ifbotech/root-kit/docs/entorno.md

# Entorno y simulador

Todo el firmware se escribe y se anima en la PC. Las placas sirven para
confirmar las tres cosas que la PC no puede decir —consumo, colores reales y
framerate— no para desarrollar.

## Qué hace falta

| Componente | Versión verificada | Para qué |
|---|---|---|
| WSL2 + Ubuntu | 24.04 LTS | Todo el firmware |
| gcc | 13.3.0 | Compilar |
| GNU Make | 4.3 | Los targets |
| SDL2 | 2.30.0 | Sólo la ventana interactiva |
| WSLg | driver x11, `DISPLAY=:0` | Mostrar esa ventana en Windows |
| clang + lld | 18 | `make wasm`: el renderer para la app |
| PlatformIO | 6.1+ | Compilar y flashear las placas (`pip install platformio`) |
| Python | 3.10+ | Convertir capturas, la estación de fábrica y el sustrato (`tools/pcb.py`) |
| OpenSCAD | 2021.01+ | Exportar el STL del sustrato. Sólo para `make pcb`: el resto se genera sin él |
| Node | 20+ | root-lab: la app, la nube y el emulador |

Las pruebas y las capturas **no necesitan SDL**: el Makefile lo detecta con
`pkg-config` y compila el simulador sin ventana si no está. Sólo `make sim` lo
pide.

**OpenSCAD tampoco es obligatorio.** `make pcb` verifica el sustrato y
regenera la plantilla, el diagrama de conexiones y la netlist con Python solo;
si OpenSCAD no está, avisa y deja el STL como estaba. En Windows está en
`C:\Program Files\OpenSCAD\openscad.exe` y se usa por línea de comandos.

```bash
cd /mnt/c/Users/ifbar/Documents/rootkit/firmware
make test
```

> **La imagen de Ubuntu viene con el índice de apt desactualizado.** Si
> instalás algo y apt tira `404 Not Found` sobre paquetes de glibc, es eso:
> corré `sudo apt update` primero. Le pasa a `build-essential` en una imagen
> recién creada, porque el índice apunta a versiones que ya salieron del pool.

En Windows hay que invocar la distro por nombre si la predeterminada es otra
(por ejemplo con Docker Desktop instalado, que registra la suya):

```bash
wsl.exe -d Ubuntu-24.04 -- bash -lc "cd /mnt/c/.../firmware && make test"
```

Y una sola vez, para que `make verify` pueda usar git desde WSL sobre `/mnt/c`:

```bash
git config --global --add safe.directory /mnt/c/Users/<vos>/Documents/rootkit
```

Sin eso git falla con `dubious ownership`. Vale la pena saber por qué el
Makefile lo comprueba explícitamente: en ese estado **git escribe el error en
stderr y aun así devuelve 0**, así que el chequeo de frescura del arte leía su
salida vacía como "no hay cambios" y pasaba en verde sin haber mirado nada. El
target ahora exige que `git rev-parse --show-toplevel` devuelva algo antes de
confiar en un `git status` vacío.

## La ventana muestra los cinco Rooties

```bash
make sim
```

Los cinco Rooties en una grilla, todos animándose con el mismo reloj sobre el
mismo mundo simulado, a 2× para que se vean en un monitor.

Eso es deliberado: lo que hay que juzgar es **si los cinco se leen como el mismo
producto y como ocho personajes distintos al mismo tiempo**. El parecido y la
diferencia sólo existen en comparación, así que con una cara por vez las dos
cosas son imposibles de evaluar.

| Tecla | Qué hace |
|---|---|
| `1`–`6` | Seleccionar modelo |
| `W` | Regar la maceta seleccionada |
| `M` | Ciclar los ánimos a la fuerza |
| `R` | Volver al ánimo real |
| `G` | Disparar el despertar del seleccionado |
| `+` / `-` | Acelerar o frenar el tiempo |
| `S` | Capturar la ventana entera a `captura.bmp` |
| `ESC` | Salir |

Un día simulado dura 48 segundos. Cada maceta tiene un ambiente que deriva
solo: la tierra se seca a su ritmo y el sol sale y se pone. Sin eso el
simulador muestra estados congelados y no se puede juzgar si las transiciones
se sienten bien.

Los seis aparatos arrancan con vínculos de distinta edad —9, 34, 62, 95, 140 y
200 días sanos— para que la ventana muestre de entrada varias etapas de
crecimiento sin tener que esperar seis meses.

## Capturas sin ventana

```bash
make sheet       # los 6 modelos x 11 ánimos
make etapas      # las 5 etapas de crecimiento, por modelo
make despertar   # los ojos se abren, por modelo
make pantallas   # QR, dormida, despertar y cara
make bench       # costo de rasterizado y cota del bus
```

Escriben BMP en `firmware/build/`. `tools/bmp2png.py` los pasa a PNG para
meterlos en el repo o mirarlos en cualquier lado.

Estos modos no abren ventana, así que corren en CI. Y son la única forma de
revisar el arte con los ojos: **la regresión visual por hash detecta que algo
cambió, no si quedó mejor o peor.**

## Por qué no hay LVGL

El plan original era usar LVGL con su port de SDL. Se descartó, y las razones
están en [decisiones.md](decisiones.md). En resumen: la cara es procedural —elipses, arcos y trazos calculados— y LVGL trae un motor
de widgets que acá no se usaría nunca; y un buffer RGB565 plano es exactamente
lo que espera `esp_lcd_panel_draw_bitmap()`, sin capa intermedia.

El renderer propio vive en `gfx/`, y el mismo código corre en el simulador, en
los tests, en las placas y, compilado a WebAssembly, en la app.

## Lo que NO se puede probar acá

Anotarlo ahora evita sorpresas cuando lleguen las placas:

- **El consumo.** Es un modelo (`nodo/power.c`). El reposo real del C3 y la
  corriente de cada retroiluminación pueden mover mucho la autonomía.
  Medidor en serie, el día uno.
- **Framerate real.** La cara con antialiasing tarda ~0,5 ms por cuadro de
  128×128 en una PC; en el C3, sin FPU y a 160 MHz, puede tardar cincuenta
  veces más. Se mide en la Fase 1.
- **Colores.** El IPS no tiene el mismo gamma que un monitor. Si salen raros,
  es el orden de bytes o de colores del panel: `RK_TFT_BGR` y
  `RK_TFT_INVERT` en `platformio.ini`.
- **Cómo se ve una cara dentro de su carcasa.** No hay forma de simularlo: hay
  que imprimir.
- **El portal cautivo en cada teléfono.** Para el resto del flujo está el
  emulador de root-lab.
