ifbotech/root-kit/hardware/pcb/generado/sustrato_datos.scad

// GENERADO por tools/pcb.py desde hardware/pcb/nucleo.json. No editar.

sustrato_ancho = 68.00;
sustrato_alto  = 92.00;
sustrato_esp   = 3.00;
canaleta_prof  = 1.20;
canaleta_holg  = 0.30;
radio_borde    = 2.00;

// [ancho, [[x,y], ...]]
canaletas = [
  [1.00, [[23.40,68.80], [23.28,68.80], [19.40,68.80], [19.40,64.55], [19.40,33.00]]],  // TFT_CS
  [1.00, [[19.40,33.00], [19.08,31.95]]],  // TFT_CS
  [1.00, [[23.40,71.40], [23.28,71.40], [14.40,71.40], [14.40,64.55], [14.40,33.00]]],  // TFT_DC
  [1.00, [[14.40,33.00], [14.00,31.95]]],  // TFT_DC
  [1.00, [[23.40,79.00], [23.28,79.00], [11.40,79.00], [11.40,64.55], [11.40,33.00]]],  // MOSI
  [1.00, [[11.40,33.00], [11.46,31.95]]],  // MOSI
  [1.00, [[23.40,81.60], [23.28,81.60], [8.80,81.60], [8.80,64.55], [8.80,33.00]]],  // SCK
  [1.00, [[8.80,33.00], [8.92,31.95]]],  // SCK
  [1.00, [[23.40,66.00], [23.28,66.00], [22.20,66.00], [22.20,64.55], [22.20,32.80], [23.28,32.80], [27.00,32.80], [27.00,13.40], [23.28,13.40], [12.80,13.40], [12.80,11.40]]],  // BL_G
  [1.00, [[12.80,11.40], [12.30,10.50]]],  // BL_G
  [1.00, [[11.40,10.00], [9.60,10.00]]],  // BL_G
  [1.00, [[9.60,10.00], [9.15,10.60]]],  // BL_G
  [1.00, [[16.40,27.00], [16.40,25.00]]],  // TFT_RST
  [1.00, [[16.40,25.00], [17.30,24.00]]],  // TFT_RST
  [1.00, [[7.40,20.00], [5.00,20.00], [5.00,20.40]]],  // BL_Q
  [1.00, [[5.00,20.40], [4.00,21.30]]],  // BL_Q
  [1.00, [[8.60,14.00], [9.40,14.00], [9.40,16.00]]],  // BL_M
  [1.00, [[9.40,16.00], [9.15,16.60]]],  // BL_M
  [1.00, [[10.00,15.60], [11.40,15.60]]],  // BL_M
  [1.00, [[11.40,15.60], [12.30,16.50]]],  // BL_M
  [1.00, [[5.00,25.20], [5.20,25.20]]],  // BL
  [1.00, [[5.20,25.20], [6.40,25.20], [6.40,27.00]]],  // BL
  [1.00, [[6.40,27.00], [6.38,28.05]]],  // BL
  [1.00, [[6.80,24.80], [9.00,24.80]]],  // BL
  [1.00, [[9.00,24.80], [10.00,24.00]]],  // BL
  [1.00, [[44.60,66.00], [44.72,66.00], [47.00,66.00]]],  // SUELO
  [1.00, [[47.00,66.00], [47.46,65.95]]],  // SUELO
  [1.00, [[44.60,69.00], [44.72,69.00], [51.40,69.00], [51.40,66.80], [55.40,66.80], [55.40,64.55], [55.40,62.60]]],  // RIEL
  [1.00, [[55.40,62.60], [56.00,61.70]]],  // RIEL
  [1.00, [[44.60,71.40], [44.72,71.40], [53.40,71.40], [53.40,71.00]]],  // SENS_EN
  [1.00, [[53.40,71.00], [54.30,70.00]]],  // SENS_EN
  [1.00, [[54.80,71.00], [54.80,73.00], [62.80,73.00], [62.80,69.80]]],  // SENS_EN
  [1.00, [[62.80,69.80], [62.80,69.60]]],  // SENS_EN
  [1.00, [[62.80,69.60], [63.40,69.15]]],  // SENS_EN
  [1.00, [[52.20,46.80], [58.00,46.80]]],  // SDA
  [1.00, [[58.00,46.80], [58.46,45.95]]],  // SDA
  [1.00, [[47.00,55.00], [47.00,50.80], [45.00,50.80]]],  // OW
  [1.00, [[45.00,50.80], [44.72,50.66], [44.00,50.30]]],  // OW
  [1.40, [[60.00,67.40], [60.00,65.00]]],  // 3V3S
  [1.00, [[60.00,65.00], [60.00,64.55], [60.00,64.00]]],  // 3V3S
  [1.40, [[61.00,63.00], [61.80,63.00], [61.80,60.60], [64.00,60.60]]],  // 3V3S
  [1.00, [[64.00,60.60], [65.00,60.30]]],  // 3V3S
  [1.00, [[55.40,83.60], [55.20,83.60]]],  // VIN
  [2.20, [[55.20,83.60], [54.80,83.60], [54.80,87.45], [54.80,88.40], [62.00,88.40]]],  // VIN
  [1.00, [[62.00,88.40], [63.00,88.00]]],  // VIN
  [2.20, [[53.80,84.60], [44.72,84.60], [44.60,84.60]]],  // VIN
  [1.00, [[44.60,84.60], [43.57,84.13]]],  // VIN
  [1.20, [[44.60,79.00], [44.72,79.00], [62.40,79.00], [62.40,75.40], [66.00,75.40], [66.00,66.60], [64.00,66.60]]],  // 3V3
  [1.00, [[64.00,66.60], [63.40,66.85]]],  // 3V3
  [1.00, [[52.80,53.00], [52.80,59.00], [44.72,59.00], [44.40,59.00], [44.40,54.60]]],  // 3V3
  [1.00, [[44.40,54.60], [44.00,53.70]]],  // 3V3
  [2.20, [[43.00,53.80], [40.40,53.80], [40.40,45.20], [43.20,45.20], [43.20,42.60], [43.60,42.60]]],  // 3V3
  [1.00, [[43.60,42.60], [43.80,42.60]]],  // 3V3
  [1.00, [[43.80,42.60], [44.19,42.05]]],  // 3V3
  [1.00, [[42.60,41.60], [41.70,42.00]]],  // 3V3
  [2.20, [[39.40,45.60], [35.40,45.60]]],  // 3V3
  [1.00, [[35.40,45.60], [34.50,45.85]]],  // 3V3
  [2.20, [[33.60,44.80], [33.60,39.00], [27.00,39.00]]],  // 3V3
  [1.00, [[27.00,39.00], [26.00,38.00]]],  // 3V3
  [1.00, [[24.20,27.00], [24.20,25.00], [23.28,25.00], [21.60,25.00]]],  // 3V3
  [1.00, [[21.60,25.00], [20.70,24.00]]],  // 3V3
  [2.20, [[20.80,23.00], [20.80,17.40], [16.60,17.40]]],  // 3V3
  [1.00, [[16.60,17.40], [15.70,16.50]]],  // 3V3
  [2.20, [[43.60,41.40], [43.60,28.40], [44.72,28.40], [53.00,28.40], [53.00,31.00]]],  // 3V3
  [1.00, [[53.00,31.00], [52.54,32.05]]],  // 3V3
  [1.00, [[53.00,33.00], [66.00,33.00], [66.00,41.00]]],  // 3V3
  [1.00, [[66.00,41.00], [66.08,42.05]]],  // 3V3
  [2.20, [[59.60,53.40], [59.60,50.20], [57.00,50.20]]],  // GND
  [1.00, [[57.00,50.20], [56.00,50.30]]],  // GND
  [1.00, [[47.20,41.00], [47.20,39.00], [63.20,39.00], [63.20,41.00]]],  // GND
  [1.00, [[63.20,41.00], [63.54,42.05]]],  // GND
  [2.20, [[28.40,49.20], [28.40,45.00], [27.00,45.00]]],  // GND
  [1.00, [[27.00,45.00], [26.00,44.00]]],  // GND
  [2.20, [[37.40,41.00], [37.40,10.20], [23.28,10.20], [16.60,10.20]]],  // GND
  [1.00, [[16.60,10.20], [15.70,10.50]]],  // GND
  [1.20, [[15.20,9.60], [15.20,7.40], [6.60,7.40], [6.60,10.00]]],  // GND
  [1.00, [[6.60,10.00], [6.85,10.60]]],  // GND
];

// [x, y, ancho, alto, rot, agujero]
pads = [
  [60.00,54.30,2.00,1.90,0.0,0.00],  // C1.1
  [60.00,57.70,2.00,1.90,0.0,0.00],  // C1.2
  [29.50,50.15,2.20,2.20,0.0,2.10],  // C2.1
  [34.50,45.85,2.20,2.20,0.0,2.10],  // C2.2
  [38.30,42.00,1.90,2.00,0.0,0.00],  // C3.1
  [41.70,42.00,1.90,2.00,0.0,0.00],  // C3.2
  [65.00,52.30,2.00,1.90,0.0,0.00],  // C4.1
  [65.00,55.70,2.00,1.90,0.0,0.00],  // C4.2
  [46.73,42.05,1.00,2.20,0.0,1.70],  // J_AIRE.GND
  [49.27,45.95,1.00,2.20,0.0,1.70],  // J_AIRE.SCL
  [51.81,45.95,1.00,2.20,0.0,1.70],  // J_AIRE.SDA
  [44.19,42.05,1.00,2.20,0.0,1.70],  // J_AIRE.VCC
  [55.92,42.05,1.00,2.20,180.0,1.70],  // J_LUZ.ADDR
  [63.54,42.05,1.00,2.20,180.0,1.70],  // J_LUZ.GND
  [61.00,45.95,1.00,2.20,180.0,1.70],  // J_LUZ.SCL
  [58.46,45.95,1.00,2.20,180.0,1.70],  // J_LUZ.SDA
  [66.08,42.05,1.00,2.20,180.0,1.70],  // J_LUZ.VCC
  [58.27,83.05,1.00,2.20,0.0,1.70],  // J_PWR.GND
  [55.73,83.05,1.00,2.20,0.0,1.70],  // J_PWR.VIN
  [47.46,65.95,1.00,2.20,0.0,1.70],  // J_SUELO.AOUT
  [50.00,62.05,1.00,2.20,0.0,1.70],  // J_SUELO.GND
  [52.54,62.05,1.00,2.20,0.0,1.70],  // J_SUELO.VCC
  [19.08,31.95,1.00,2.20,180.0,1.70],  // J_TFT.CS
  [14.00,31.95,1.00,2.20,180.0,1.70],  // J_TFT.DC
  [21.62,28.05,1.00,2.20,180.0,1.70],  // J_TFT.GND
  [6.38,28.05,1.00,2.20,180.0,1.70],  // J_TFT.LED
  [16.54,28.05,1.00,2.20,180.0,1.70],  // J_TFT.RESET
  [8.92,31.95,1.00,2.20,180.0,1.70],  // J_TFT.SCK
  [11.46,31.95,1.00,2.20,180.0,1.70],  // J_TFT.SDI
  [3.84,28.05,1.00,2.20,180.0,1.70],  // J_TFT.SDO
  [24.16,28.05,1.00,2.20,180.0,1.70],  // J_TFT.VCC
  [47.46,55.95,1.00,2.20,0.0,1.70],  // J_TIERRA.DQ
  [50.00,52.05,1.00,2.20,0.0,1.70],  // J_TIERRA.GND
  [52.54,52.05,1.00,2.20,0.0,1.70],  // J_TIERRA.VCC
  [50.00,32.05,1.00,2.20,0.0,1.70],  // J_TOQUE.GND
  [47.46,35.95,1.00,2.20,0.0,1.70],  // J_TOQUE.IO
  [52.54,32.05,1.00,2.20,0.0,1.70],  // J_TOQUE.VCC
  [60.60,68.00,1.20,1.40,270.0,0.00],  // Q2.D
  [63.40,69.15,1.20,1.40,270.0,0.00],  // Q2.G
  [63.40,66.85,1.20,1.40,270.0,0.00],  // Q2.S
  [8.00,13.40,1.20,1.40,180.0,0.00],  // Q3.D
  [9.15,10.60,1.20,1.40,180.0,0.00],  // Q3.G
  [6.85,10.60,1.20,1.40,180.0,0.00],  // Q3.S
  [8.00,19.40,1.20,1.40,180.0,0.00],  // Q4.D
  [9.15,16.60,1.20,1.40,180.0,0.00],  // Q4.G
  [6.85,16.60,1.20,1.40,180.0,0.00],  // Q4.S
  [56.00,58.30,2.00,1.90,0.0,0.00],  // R1.1
  [56.00,61.70,2.00,1.90,0.0,0.00],  // R1.2
  [4.00,21.30,2.00,1.90,0.0,0.00],  // R11.1
  [4.00,24.70,2.00,1.90,0.0,0.00],  // R11.2
  [56.00,50.30,2.00,1.90,0.0,0.00],  // R2.1
  [56.00,53.70,2.00,1.90,0.0,0.00],  // R2.2
  [54.30,70.00,1.90,2.00,0.0,0.00],  // R4.1
  [57.70,70.00,1.90,2.00,0.0,0.00],  // R4.2
  [65.00,60.30,2.00,1.90,0.0,0.00],  // R5.1
  [65.00,63.70,2.00,1.90,0.0,0.00],  // R5.2
  [44.00,50.30,2.00,1.90,0.0,0.00],  // R6.1
  [44.00,53.70,2.00,1.90,0.0,0.00],  // R6.2
  [17.30,24.00,1.90,2.00,0.0,0.00],  // R7.1
  [20.70,24.00,1.90,2.00,0.0,0.00],  // R7.2
  [12.30,10.50,1.90,2.00,0.0,0.00],  // R8.1
  [15.70,10.50,1.90,2.00,0.0,0.00],  // R8.2
  [12.30,16.50,1.90,2.00,0.0,0.00],  // R9.1
  [15.70,16.50,1.90,2.00,0.0,0.00],  // R9.2
  [26.00,44.00,2.20,2.20,0.0,0.00],  // TP1.1
  [63.00,88.00,2.20,2.20,0.0,0.00],  // TP2.1
  [26.00,38.00,2.20,2.20,0.0,0.00],  // TP3.1
  [60.00,64.00,2.20,2.20,0.0,0.00],  // TP4.1
  [10.00,24.00,2.20,2.20,0.0,0.00],  // TP5.1
  [43.57,79.05,2.20,1.00,0.0,1.70],  // U1.3V3
  [43.57,84.13,2.20,1.00,0.0,1.70],  // U1.5V
  [43.57,81.59,2.20,1.00,0.0,1.70],  // U1.GND
  [43.57,66.35,2.20,1.00,0.0,1.70],  // U1.IO0
  [43.57,68.89,2.20,1.00,0.0,1.70],  // U1.IO1
  [24.43,71.43,2.20,1.00,0.0,1.70],  // U1.IO10
  [43.57,71.43,2.20,1.00,0.0,1.70],  // U1.IO2
  [24.43,68.89,2.20,1.00,0.0,1.70],  // U1.IO20
  [24.43,66.35,2.20,1.00,0.0,1.70],  // U1.IO21
  [43.57,73.97,2.20,1.00,0.0,1.70],  // U1.IO3
  [43.57,76.51,2.20,1.00,0.0,1.70],  // U1.IO4
  [24.43,84.13,2.20,1.00,0.0,1.70],  // U1.IO5
  [24.43,81.59,2.20,1.00,0.0,1.70],  // U1.IO6
  [24.43,79.05,2.20,1.00,0.0,1.70],  // U1.IO7
  [24.43,76.51,2.20,1.00,0.0,1.70],  // U1.IO8
  [24.43,73.97,2.20,1.00,0.0,1.70],  // U1.IO9
];

// [centro x, centro y, ancho, alto] — aberturas pasantes
recortes = [
  [34.00,87.67,9.00,9.00],  // antena
];

// [x, y, diametro]
tornillos = [
  [3.00,11.00,2.70],
  [65.00,11.00,2.70],
  [3.00,81.00,2.70],
  [65.00,81.00,2.70],
];

// --- la estampadora (el negativo, espejado en X) ---
est_holgura_lateral = 0.20;
est_sobresalir     = 1.00;
est_base_extra     = 0.20;
est_base_alto      = 0.25;
est_espesor        = 5.00;
est_faldon_alto    = 3.50;
est_faldon_pared   = 2.00;
est_faldon_holgura = 0.50;
est_relieve_hueco  = 0.60;
est_rotulo_tam   = 5.00;
est_rotulo       = "ESTAMPADORA v3.1";

// [x, y, tamano, rot, "texto"]
rotulos = [
  [31.00,58.00,2.00,0.0,"ROOTKIT v3.0"],
  [31.00,53.50,1.60,0.0,"ifbotech"],
];
