ifbotech/root-kit/firmware/esp32/certificados.h

/* certificados.h — las raíces en las que confía la placa para hablar con la nube.
 *
 * GENERADO a partir del almacén de certificados de Ubuntu y de
 * letsencrypt.org/certificates. Ver docs/firmware.md, "La nube por HTTPS".
 *
 * El servidor de ROOTLAB (Caddy) saca sus certificados de Let's Encrypt y,
 * si Let's Encrypt falla, de ZeroSSL. La placa confía SOLO en las raíces de
 * esas dos autoridades: un certificado de cualquier otra —aunque un
 * navegador lo acepte— no alcanza para hacerse pasar por la nube.
 *
 * Van también las raíces de la generación siguiente de Let's Encrypt (Root
 * YE y YR): una placa se queda años en una casa, y tiene que seguir
 * conectándose cuando cambie la cadena.
 *
 * Huellas SHA-256, para verificar contra las que publica cada autoridad:
 *
 *   ISRG Root X1 (Let's Encrypt, RSA, vence 2035)
 *     96:BC:EC:06:26:49:76:F3:74:60:77:9A:CF:28:C5:A7:CF:E8:A3:C0:AA:E1:1A:8F:FC:EE:05:C0:BD:DF:08:C6
 *   ISRG Root X2 (Let's Encrypt, ECDSA, vence 2040)
 *     69:72:9B:8E:15:A8:6E:FC:17:7A:57:AF:B7:17:1D:FC:64:AD:D2:8C:2F:CA:8C:F1:50:7E:34:45:3C:CB:14:70
 *   ISRG Root YE (Let's Encrypt, generacion Y, ECDSA, vence 2045)
 *     E1:4F:FC:AD:5B:00:25:73:10:06:CA:A4:3A:12:1A:22:D8:E9:70:0F:4F:B9:CF:85:2F:02:A7:08:AA:5D:56:66
 *   ISRG Root YR (Let's Encrypt, generacion Y, RSA, vence 2045)
 *     E5:7B:7E:6F:15:0C:41:91:02:E8:D5:C0:55:72:9F:F9:67:B9:D1:A8:29:BF:00:CE:C8:9C:A6:04:EB:F4:A8:6F
 *   USERTrust ECC (ZeroSSL, la CA de respaldo de Caddy, vence 2038)
 *     4F:F4:60:D5:4B:9C:86:DA:BF:BC:FC:57:12:E0:40:0D:2B:ED:3F:BC:4D:4F:BD:AA:86:E0:6A:DC:D2:A9:AD:7A
 *   USERTrust RSA (ZeroSSL, vence 2038)
 *     E7:93:C9:B0:2F:D8:AA:13:E2:1C:31:22:8A:CC:B0:81:19:64:3B:74:9C:89:89:64:B1:74:6D:46:C3:D4:CB:D2
 */
#ifndef ROOTKIT_CERTIFICADOS_H
#define ROOTKIT_CERTIFICADOS_H

static const char RK_CA_RAICES[] =
    /* ISRG Root X1 (Let's Encrypt, RSA, vence 2035) */
    "-----BEGIN CERTIFICATE-----\n"
    "MIIFazCCA1OgAwIBAgIRAIIQz7DSQONZRGPgu2OCiwAwDQYJKoZIhvcNAQELBQAw\n"
    "TzELMAkGA1UEBhMCVVMxKTAnBgNVBAoTIEludGVybmV0IFNlY3VyaXR5IFJlc2Vh\n"
    "cmNoIEdyb3VwMRUwEwYDVQQDEwxJU1JHIFJvb3QgWDEwHhcNMTUwNjA0MTEwNDM4\n"
    "WhcNMzUwNjA0MTEwNDM4WjBPMQswCQYDVQQGEwJVUzEpMCcGA1UEChMgSW50ZXJu\n"
    "ZXQgU2VjdXJpdHkgUmVzZWFyY2ggR3JvdXAxFTATBgNVBAMTDElTUkcgUm9vdCBY\n"
    "MTCCAiIwDQYJKoZIhvcNAQEBBQADggIPADCCAgoCggIBAK3oJHP0FDfzm54rVygc\n"
    "h77ct984kIxuPOZXoHj3dcKi/vVqbvYATyjb3miGbESTtrFj/RQSa78f0uoxmyF+\n"
    "0TM8ukj13Xnfs7j/EvEhmkvBioZxaUpmZmyPfjxwv60pIgbz5MDmgK7iS4+3mX6U\n"
    "A5/TR5d8mUgjU+g4rk8Kb4Mu0UlXjIB0ttov0DiNewNwIRt18jA8+o+u3dpjq+sW\n"
    "T8KOEUt+zwvo/7V3LvSye0rgTBIlDHCNAymg4VMk7BPZ7hm/ELNKjD+Jo2FR3qyH\n"
    "B5T0Y3HsLuJvW5iB4YlcNHlsdu87kGJ55tukmi8mxdAQ4Q7e2RCOFvu396j3x+UC\n"
    "B5iPNgiV5+I3lg02dZ77DnKxHZu8A/lJBdiB3QW0KtZB6awBdpUKD9jf1b0SHzUv\n"
    "KBds0pjBqAlkd25HN7rOrFleaJ1/ctaJxQZBKT5ZPt0m9STJEadao0xAH0ahmbWn\n"
    "OlFuhjuefXKnEgV4We0+UXgVCwOPjdAvBbI+e0ocS3MFEvzG6uBQE3xDk3SzynTn\n"
    "jh8BCNAw1FtxNrQHusEwMFxIt4I7mKZ9YIqioymCzLq9gwQbooMDQaHWBfEbwrbw\n"
    "qHyGO0aoSCqI3Haadr8faqU9GY/rOPNk3sgrDQoo//fb4hVC1CLQJ13hef4Y53CI\n"
    "rU7m2Ys6xt0nUW7/vGT1M0NPAgMBAAGjQjBAMA4GA1UdDwEB/wQEAwIBBjAPBgNV\n"
    "HRMBAf8EBTADAQH/MB0GA1UdDgQWBBR5tFnme7bl5AFzgAiIyBpY9umbbjANBgkq\n"
    "hkiG9w0BAQsFAAOCAgEAVR9YqbyyqFDQDLHYGmkgJykIrGF1XIpu+ILlaS/V9lZL\n"
    "ubhzEFnTIZd+50xx+7LSYK05qAvqFyFWhfFQDlnrzuBZ6brJFe+GnY+EgPbk6ZGQ\n"
    "3BebYhtF8GaV0nxvwuo77x/Py9auJ/GpsMiu/X1+mvoiBOv/2X/qkSsisRcOj/KK\n"
    "NFtY2PwByVS5uCbMiogziUwthDyC3+6WVwW6LLv3xLfHTjuCvjHIInNzktHCgKQ5\n"
    "ORAzI4JMPJ+GslWYHb4phowim57iaztXOoJwTdwJx4nLCgdNbOhdjsnvzqvHu7Ur\n"
    "TkXWStAmzOVyyghqpZXjFaH3pO3JLF+l+/+sKAIuvtd7u+Nxe5AW0wdeRlN8NwdC\n"
    "jNPElpzVmbUq4JUagEiuTDkHzsxHpFKVK7q4+63SM1N95R1NbdWhscdCb+ZAJzVc\n"
    "oyi3B43njTOQ5yOf+1CceWxG1bQVs5ZufpsMljq4Ui0/1lvh+wjChP4kqKOJ2qxq\n"
    "4RgqsahDYVvTH9w7jXbyLeiNdd8XM2w9U/t7y0Ff/9yi0GE44Za4rF2LN9d11TPA\n"
    "mRGunUHBcnWEvgJBQl9nJEiU0Zsnvgc/ubhPgXRR4Xq37Z0j4r7g1SgEEzwxA57d\n"
    "emyPxgcYxn/eR44/KJ4EBs+lVDR3veyJm+kXQ99b21/+jh5Xos1AnX5iItreGCc=\n"
    "-----END CERTIFICATE-----\n"
    /* ISRG Root X2 (Let's Encrypt, ECDSA, vence 2040) */
    "-----BEGIN CERTIFICATE-----\n"
    "MIICGzCCAaGgAwIBAgIQQdKd0XLq7qeAwSxs6S+HUjAKBggqhkjOPQQDAzBPMQsw\n"
    "CQYDVQQGEwJVUzEpMCcGA1UEChMgSW50ZXJuZXQgU2VjdXJpdHkgUmVzZWFyY2gg\n"
    "R3JvdXAxFTATBgNVBAMTDElTUkcgUm9vdCBYMjAeFw0yMDA5MDQwMDAwMDBaFw00\n"
    "MDA5MTcxNjAwMDBaME8xCzAJBgNVBAYTAlVTMSkwJwYDVQQKEyBJbnRlcm5ldCBT\n"
    "ZWN1cml0eSBSZXNlYXJjaCBHcm91cDEVMBMGA1UEAxMMSVNSRyBSb290IFgyMHYw\n"
    "EAYHKoZIzj0CAQYFK4EEACIDYgAEzZvVn4CDCuwJSvMWSj5cz3es3mcFDR0HttwW\n"
    "+1qLFNvicWDEukWVEYmO6gbf9yoWHKS5xcUy4APgHoIYOIvXRdgKam7mAHf7AlF9\n"
    "ItgKbppbd9/w+kHsOdx1ymgHDB/qo0IwQDAOBgNVHQ8BAf8EBAMCAQYwDwYDVR0T\n"
    "AQH/BAUwAwEB/zAdBgNVHQ4EFgQUfEKWrt5LSDv6kviejM9ti6lyN5UwCgYIKoZI\n"
    "zj0EAwMDaAAwZQIwe3lORlCEwkSHRhtFcP9Ymd70/aTSVaYgLXTWNLxBo1BfASdW\n"
    "tL4ndQavEi51mI38AjEAi/V3bNTIZargCyzuFJ0nN6T5U6VR5CmD1/iQMVtCnwr1\n"
    "/q4AaOeMSQ+2b1tbFfLn\n"
    "-----END CERTIFICATE-----\n"
    /* ISRG Root YE (Let's Encrypt, generacion Y, ECDSA, vence 2045) */
    "-----BEGIN CERTIFICATE-----\n"
    "MIIB2TCCAWCgAwIBAgIRAKQCa6LvbHwg1AR+XmWmk4AwCgYIKoZIzj0EAwMwLjEL\n"
    "MAkGA1UEBhMCVVMxDTALBgNVBAoTBElTUkcxEDAOBgNVBAMTB1Jvb3QgWUUwHhcN\n"
    "MjUwOTAzMDAwMDAwWhcNNDUwOTAyMjM1OTU5WjAuMQswCQYDVQQGEwJVUzENMAsG\n"
    "A1UEChMESVNSRzEQMA4GA1UEAxMHUm9vdCBZRTB2MBAGByqGSM49AgEGBSuBBAAi\n"
    "A2IABDwS/6vhrcVqcbBo+wgdI3fwn9x7DNJJOY/lTOti0vkwuRN87RhEhTH17E7X\n"
    "yFjWsPYhIPt/wzOqxTd2b+4ZJNy9ID04YywF9U5zasDVyGSNErVNtz8uSGh5izW8\n"
    "7j77GaNCMEAwDgYDVR0PAQH/BAQDAgEGMA8GA1UdEwEB/wQFMAMBAf8wHQYDVR0O\n"
    "BBYEFKPIJlqOoUzQNWP8myPIOq5W809WMAoGCCqGSM49BAMDA2cAMGQCMHhMr8N9\n"
    "LdL1VQKs9BdV81r76eXRB6mtjuNjzk6/lBsPNToWLTDzGYgtQKO1jl63uAIwGV7m\n"
    "onyF377c+MM1oqVNs17sgu7F9YKZwgLmVbeOMDbKAXHtKMDLbiGllCcs8f47\n"
    "-----END CERTIFICATE-----\n"
    /* ISRG Root YR (Let's Encrypt, generacion Y, RSA, vence 2045) */
    "-----BEGIN CERTIFICATE-----\n"
    "MIIFKTCCAxGgAwIBAgIRAOxGNJNgz0sP+KmC2Tqpyj0wDQYJKoZIhvcNAQELBQAw\n"
    "LjELMAkGA1UEBhMCVVMxDTALBgNVBAoTBElTUkcxEDAOBgNVBAMTB1Jvb3QgWVIw\n"
    "HhcNMjUwOTAzMDAwMDAwWhcNNDUwOTAyMjM1OTU5WjAuMQswCQYDVQQGEwJVUzEN\n"
    "MAsGA1UEChMESVNSRzEQMA4GA1UEAxMHUm9vdCBZUjCCAiIwDQYJKoZIhvcNAQEB\n"
    "BQADggIPADCCAgoCggIBANvGJnN78CTJdWL3+eGfsLN5TrNBJs+VH9hRXqRbwxu9\n"
    "sGNiB0BD1fcOxbSUQCJIM1xE13Db+5Cw1w0s0EBYsvuIP/6joF0w8cuImbgR1OGg\n"
    "YbSQ4OpzI+DG8SGuTlcE873OCS+kh3srlo6vl43M5OJg4Aeo1sfHp6kTJDoIiFBN\n"
    "JAY+OKfX/FUvYKuhjT+no49lmqmupSBI5PkBQiqrEGtWU5uxU/cQWHGu8jSjFBzn\n"
    "ZqvbNPLMXMLFxCb3WTfrJBXXjqvWG+v4bjzxjjeAtOlU7qarRDvNOyAuQYLln904\n"
    "M+faKx8hnLCpJ15ZqaEgcNlY+9MMWcC5yvL2A2j3l9+2buggZX+dOE91zYmIdawT\n"
    "vSZuVvlbRrAlLxIB6pwMBjneXCjYQ8+3BCCjssbSNpZU3hTcBDdhfAlEDlYr6pEa\n"
    "tnMdmDT5BqnKC92bd0EhM1fbLHioLccLCuievT8ZkPhZrq7Mii7gNXAcUEAR8+lz\n"
    "Yal+9zTg7C5DALyVOeG/CqfRAMn1KSHCR0NSA6P8tn/mGRlnCct5rtVCLnVySVpU\n"
    "6H1qGg3DgTOuskf8eahTMiYbI5ezPJmO5ertalskQ1utp74+eDy92PI4ftHKTbq9\n"
    "IWhH4YZKh3WnJEIt+oQvlYZbY8tpEroKrFB6PFGzrJIDRyts4HqvuH52RFj2zv/B\n"
    "AgMBAAGjQjBAMA4GA1UdDwEB/wQEAwIBBjAPBgNVHRMBAf8EBTADAQH/MB0GA1Ud\n"
    "DgQWBBTe51tg0CJtQCh9Pw0B/qS1UrRRlDANBgkqhkiG9w0BAQsFAAOCAgEAWHnf\n"
    "713Bdkq7t5yN2dNIgQakUb94X9WuyhMEHHkgx4oDpSUlnG0w4g94MoqaEUE31ZjR\n"
    "LU7L5LD1g9ujFHTQu8AD215AHMVQFbm6j8hQxdXHAzDajFNQnOlDJrLjzIx176oy\n"
    "AjvUtejZx2NNmdb5fd0WGVGsCdoAJ3N8ozo7ajE8t6vfxStZb4BQ9WYJGHUDrv2N\n"
    "i5tJF6CNiPnlzs3BUfECRbE4JSk+jvy8+VoGiFE8qsH/j78x2fjgQhAQFV7P7Zxy\n"
    "dBTZ1wEkNpZNW2qnaK1SKBLa+xf6E06YRIq5uaI+HWH8SY1y5VbRgzq40EKg3yxP\n"
    "06fz+uYAUIFJoLNfhwRCc3Q6pQVuMX3yAjHAes4gk4moGcLQ5p7HAh39yeylZc1J\n"
    "41sx/jKwLIkPE6Rr1Nf4pxdsxf9SA4yOEiAkDgq04DVxn8hgYFdUtBCuiuVC2heA\n"
    "EiqVEa+8QZjuw8Gj0EbHXcRd1nInvGqRS1o9Is7YBdQN57X1AYveGBNNqjICSb7c\n"
    "awuw1EawTDrs13VUlJVEsbQ0/O/1aaV73mCdOQ8azqL2KTv1Ewu1xbquE2S+kdQU\n"
    "To9TUwat3wUA6cwXh1EfpS/3fJ0aGah5hdpRyoCLDlsSn8tkrjMfFFX0viC+GxHc\n"
    "sI1ANRYvqSFC2X1VRZfDg+wD6E21BccmifG4yWc=\n"
    "-----END CERTIFICATE-----\n"
    /* USERTrust ECC (ZeroSSL, la CA de respaldo de Caddy, vence 2038) */
    "-----BEGIN CERTIFICATE-----\n"
    "MIICjzCCAhWgAwIBAgIQXIuZxVqUxdJxVt7NiYDMJjAKBggqhkjOPQQDAzCBiDEL\n"
    "MAkGA1UEBhMCVVMxEzARBgNVBAgTCk5ldyBKZXJzZXkxFDASBgNVBAcTC0plcnNl\n"
    "eSBDaXR5MR4wHAYDVQQKExVUaGUgVVNFUlRSVVNUIE5ldHdvcmsxLjAsBgNVBAMT\n"
    "JVVTRVJUcnVzdCBFQ0MgQ2VydGlmaWNhdGlvbiBBdXRob3JpdHkwHhcNMTAwMjAx\n"
    "MDAwMDAwWhcNMzgwMTE4MjM1OTU5WjCBiDELMAkGA1UEBhMCVVMxEzARBgNVBAgT\n"
    "Ck5ldyBKZXJzZXkxFDASBgNVBAcTC0plcnNleSBDaXR5MR4wHAYDVQQKExVUaGUg\n"
    "VVNFUlRSVVNUIE5ldHdvcmsxLjAsBgNVBAMTJVVTRVJUcnVzdCBFQ0MgQ2VydGlm\n"
    "aWNhdGlvbiBBdXRob3JpdHkwdjAQBgcqhkjOPQIBBgUrgQQAIgNiAAQarFRaqflo\n"
    "I+d61SRvU8Za2EurxtW20eZzca7dnNYMYf3boIkDuAUU7FfO7l0/4iGzzvfUinng\n"
    "o4N+LZfQYcTxmdwlkWOrfzCjtHDix6EznPO/LlxTsV+zfTJ/ijTjeXmjQjBAMB0G\n"
    "A1UdDgQWBBQ64QmG1M8ZwpZ2dEl23OA1xmNjmjAOBgNVHQ8BAf8EBAMCAQYwDwYD\n"
    "VR0TAQH/BAUwAwEB/zAKBggqhkjOPQQDAwNoADBlAjA2Z6EWCNzklwBBHU6+4WMB\n"
    "zzuqQhFkoJ2UOQIReVx7Hfpkue4WQrO/isIJxOzksU0CMQDpKmFHjFJKS04YcPbW\n"
    "RNZu9YO6bVi9JNlWSOrvxKJGgYhqOkbRqZtNyWHa0V1Xahg=\n"
    "-----END CERTIFICATE-----\n"
    /* USERTrust RSA (ZeroSSL, vence 2038) */
    "-----BEGIN CERTIFICATE-----\n"
    "MIIF3jCCA8agAwIBAgIQAf1tMPyjylGoG7xkDjUDLTANBgkqhkiG9w0BAQwFADCB\n"
    "iDELMAkGA1UEBhMCVVMxEzARBgNVBAgTCk5ldyBKZXJzZXkxFDASBgNVBAcTC0pl\n"
    "cnNleSBDaXR5MR4wHAYDVQQKExVUaGUgVVNFUlRSVVNUIE5ldHdvcmsxLjAsBgNV\n"
    "BAMTJVVTRVJUcnVzdCBSU0EgQ2VydGlmaWNhdGlvbiBBdXRob3JpdHkwHhcNMTAw\n"
    "MjAxMDAwMDAwWhcNMzgwMTE4MjM1OTU5WjCBiDELMAkGA1UEBhMCVVMxEzARBgNV\n"
    "BAgTCk5ldyBKZXJzZXkxFDASBgNVBAcTC0plcnNleSBDaXR5MR4wHAYDVQQKExVU\n"
    "aGUgVVNFUlRSVVNUIE5ldHdvcmsxLjAsBgNVBAMTJVVTRVJUcnVzdCBSU0EgQ2Vy\n"
    "dGlmaWNhdGlvbiBBdXRob3JpdHkwggIiMA0GCSqGSIb3DQEBAQUAA4ICDwAwggIK\n"
    "AoICAQCAEmUXNg7D2wiz0KxXDXbtzSfTTK1Qg2HiqiBNCS1kCdzOiZ/MPans9s/B\n"
    "3PHTsdZ7NygRK0faOca8Ohm0X6a9fZ2jY0K2dvKpOyuR+OJv0OwWIJAJPuLodMkY\n"
    "tJHUYmTbf6MG8YgYapAiPLz+E/CHFHv25B+O1ORRxhFnRghRy4YUVD+8M/5+bJz/\n"
    "Fp0YvVGONaanZshyZ9shZrHUm3gDwFA66Mzw3LyeTP6vBZY1H1dat//O+T23LLb2\n"
    "VN3I5xI6Ta5MirdcmrS3ID3KfyI0rn47aGYBROcBTkZTmzNg95S+UzeQc0PzMsNT\n"
    "79uq/nROacdrjGCT3sTHDN/hMq7MkztReJVni+49Vv4M0GkPGw/zJSZrM233bkf6\n"
    "c0Plfg6lZrEpfDKEY1WJxA3Bk1QwGROs0303p+tdOmw1XNtB1xLaqUkL39iAigmT\n"
    "Yo61Zs8liM2EuLE/pDkP2QKe6xJMlXzzawWpXhaDzLhn4ugTncxbgtNMs+1b/97l\n"
    "c6wjOy0AvzVVdAlJ2ElYGn+SNuZRkg7zJn0cTRe8yexDJtC/QV9AqURE9JnnV4ee\n"
    "UB9XVKg+/XRjL7FQZQnmWEIuQxpMtPAlR1n6BB6T1CZGSlCBst6+eLf8ZxXhyVeE\n"
    "Hg9j1uliutZfVS7qXMYoCAQlObgOK6nyTJccBz8NUvXt7y+CDwIDAQABo0IwQDAd\n"
    "BgNVHQ4EFgQUU3m/WqorSs9UgOHYm8Cd8rIDZsswDgYDVR0PAQH/BAQDAgEGMA8G\n"
    "A1UdEwEB/wQFMAMBAf8wDQYJKoZIhvcNAQEMBQADggIBAFzUfA3P9wF9QZllDHPF\n"
    "Up/L+M+ZBn8b2kMVn54CVVeWFPFSPCeHlCjtHzoBN6J2/FNQwISbxmtOuowhT6KO\n"
    "VWKR82kV2LyI48SqC/3vqOlLVSoGIG1VeCkZ7l8wXEskEVX/JJpuXior7gtNn3/3\n"
    "ATiUFJVDBwn7YKnuHKsSjKCaXqeYalltiz8I+8jRRa8YFWSQEg9zKC7F4iRO/Fjs\n"
    "8PRF/iKz6y+O0tlFYQXBl2+odnKPi4w2r78NBc5xjeambx9spnFixdjQg3IM8WcR\n"
    "iQycE0xyNN+81XHfqnHd4blsjDwSXWXavVcStkNr/+XeTWYRUc+ZruwXtuhxkYze\n"
    "Sf7dNXGiFSeUHM9h4ya7b6NnJSFd5t0dCy5oGzuCr+yDZ4XUmFF0sbmZgIn/f3gZ\n"
    "XHlKYC6SQK5MNyosycdiyA5d9zZbyuAlJQG03RoHnHcAP9Dc1ew91Pq7P8yF1m9/\n"
    "qS3fuQL39ZeatTXaw2ewh0qpKJ4jjv9cJ2vhsE/zB+4ALtRZh8tSQZXq9EfX7mRB\n"
    "VXyNWQKV3WKdwrnuWih0hKWbt5DHDAff9Yk2dDLWKMGwsAvgnEzDHNb842m1R0aB\n"
    "L6KCq9NjRHDEjf8tM7qtj3u1cIiuPhnPQCjY/MiQu12ZIvVS5ljFH4gxQ+6IHdfG\n"
    "jjxDah2nGN59PRbxYvnKkKj9\n"
    "-----END CERTIFICATE-----\n";

#endif /* ROOTKIT_CERTIFICADOS_H */
