ifbotech/root-kit/firmware/core/sha256.c

#include "sha256.h"
#include <string.h>

static const uint32_t K[64] = {
    0x428a2f98u, 0x71374491u, 0xb5c0fbcfu, 0xe9b5dba5u, 0x3956c25bu, 0x59f111f1u,
    0x923f82a4u, 0xab1c5ed5u, 0xd807aa98u, 0x12835b01u, 0x243185beu, 0x550c7dc3u,
    0x72be5d74u, 0x80deb1feu, 0x9bdc06a7u, 0xc19bf174u, 0xe49b69c1u, 0xefbe4786u,
    0x0fc19dc6u, 0x240ca1ccu, 0x2de92c6fu, 0x4a7484aau, 0x5cb0a9dcu, 0x76f988dau,
    0x983e5152u, 0xa831c66du, 0xb00327c8u, 0xbf597fc7u, 0xc6e00bf3u, 0xd5a79147u,
    0x06ca6351u, 0x14292967u, 0x27b70a85u, 0x2e1b2138u, 0x4d2c6dfcu, 0x53380d13u,
    0x650a7354u, 0x766a0abbu, 0x81c2c92eu, 0x92722c85u, 0xa2bfe8a1u, 0xa81a664bu,
    0xc24b8b70u, 0xc76c51a3u, 0xd192e819u, 0xd6990624u, 0xf40e3585u, 0x106aa070u,
    0x19a4c116u, 0x1e376c08u, 0x2748774cu, 0x34b0bcb5u, 0x391c0cb3u, 0x4ed8aa4au,
    0x5b9cca4fu, 0x682e6ff3u, 0x748f82eeu, 0x78a5636fu, 0x84c87814u, 0x8cc70208u,
    0x90befffau, 0xa4506cebu, 0xbef9a3f7u, 0xc67178f2u
};

#define ROTR(x, n) (((x) >> (n)) | ((x) << (32 - (n))))

static void bloque(rk_sha256_t *s, const uint8_t *p)
{
    uint32_t w[64], a, b, c, d, e, f, g, h, t1, t2;
    int i;

    for (i = 0; i < 16; i++) {
        w[i] = ((uint32_t)p[i * 4] << 24) | ((uint32_t)p[i * 4 + 1] << 16) |
               ((uint32_t)p[i * 4 + 2] << 8) | (uint32_t)p[i * 4 + 3];
    }
    for (i = 16; i < 64; i++) {
        uint32_t s0 = ROTR(w[i - 15], 7) ^ ROTR(w[i - 15], 18) ^ (w[i - 15] >> 3);
        uint32_t s1 = ROTR(w[i - 2], 17) ^ ROTR(w[i - 2], 19) ^ (w[i - 2] >> 10);
        w[i] = w[i - 16] + s0 + w[i - 7] + s1;
    }
    a = s->h[0]; b = s->h[1]; c = s->h[2]; d = s->h[3];
    e = s->h[4]; f = s->h[5]; g = s->h[6]; h = s->h[7];
    for (i = 0; i < 64; i++) {
        t1 = h + (ROTR(e, 6) ^ ROTR(e, 11) ^ ROTR(e, 25)) + ((e & f) ^ (~e & g)) + K[i] + w[i];
        t2 = (ROTR(a, 2) ^ ROTR(a, 13) ^ ROTR(a, 22)) + ((a & b) ^ (a & c) ^ (b & c));
        h = g; g = f; f = e; e = d + t1;
        d = c; c = b; b = a; a = t1 + t2;
    }
    s->h[0] += a; s->h[1] += b; s->h[2] += c; s->h[3] += d;
    s->h[4] += e; s->h[5] += f; s->h[6] += g; s->h[7] += h;
}

void rk_sha256_init(rk_sha256_t *s)
{
    static const uint32_t H0[8] = {
        0x6a09e667u, 0xbb67ae85u, 0x3c6ef372u, 0xa54ff53au,
        0x510e527fu, 0x9b05688cu, 0x1f83d9abu, 0x5be0cd19u
    };
    memcpy(s->h, H0, sizeof H0);
    s->bits = 0u;
    s->n = 0u;
}

void rk_sha256_update(rk_sha256_t *s, const uint8_t *data, size_t len)
{
    size_t i;
    for (i = 0; i < len; i++) {
        s->buf[s->n++] = data[i];
        if (s->n == 64u) {
            bloque(s, s->buf);
            s->bits += 512u;
            s->n = 0u;
        }
    }
}

void rk_sha256_final(rk_sha256_t *s, uint8_t out[RK_SHA256_LEN])
{
    uint64_t bits = s->bits + (uint64_t)s->n * 8u;
    uint8_t pad = 0x80u, cero = 0u, len[8];
    int i;

    rk_sha256_update(s, &pad, 1u);
    while (s->n != 56u) {
        rk_sha256_update(s, &cero, 1u);
    }
    for (i = 0; i < 8; i++) {
        len[i] = (uint8_t)(bits >> (56 - 8 * i));
    }
    rk_sha256_update(s, len, 8u);
    for (i = 0; i < 8; i++) {
        out[i * 4]     = (uint8_t)(s->h[i] >> 24);
        out[i * 4 + 1] = (uint8_t)(s->h[i] >> 16);
        out[i * 4 + 2] = (uint8_t)(s->h[i] >> 8);
        out[i * 4 + 3] = (uint8_t)(s->h[i]);
    }
}

void rk_sha256(const uint8_t *data, size_t len, uint8_t out[RK_SHA256_LEN])
{
    rk_sha256_t s;
    rk_sha256_init(&s);
    rk_sha256_update(&s, data, len);
    rk_sha256_final(&s, out);
}

void rk_hmac_sha256(const uint8_t *key, size_t key_len,
                    const uint8_t *msg, size_t msg_len,
                    uint8_t out[RK_SHA256_LEN])
{
    uint8_t k[64], ipad[64], opad[64], interno[RK_SHA256_LEN];
    rk_sha256_t s;
    int i;

    memset(k, 0, sizeof k);
    if (key_len > 64u) {
        rk_sha256(key, key_len, k);
    } else if (key_len > 0u) {
        memcpy(k, key, key_len);
    }
    for (i = 0; i < 64; i++) {
        ipad[i] = (uint8_t)(k[i] ^ 0x36u);
        opad[i] = (uint8_t)(k[i] ^ 0x5cu);
    }
    rk_sha256_init(&s);
    rk_sha256_update(&s, ipad, 64u);
    rk_sha256_update(&s, msg, msg_len);
    rk_sha256_final(&s, interno);

    rk_sha256_init(&s);
    rk_sha256_update(&s, opad, 64u);
    rk_sha256_update(&s, interno, RK_SHA256_LEN);
    rk_sha256_final(&s, out);
}
