ifbotech/root-kit/firmware/test/main.c

/* Corredor de pruebas de ROOTKIT.
 *
 *   make test          corre todo
 *   ./build/rk_test    lo mismo, directo
 *
 * Devuelve 0 si está todo en verde, 1 si algo falló, que es lo que mira CI.
 */
#include <stdio.h>
#include "rk_test.h"

int main(void)
{
    printf("\n  ROOTKIT — pruebas\n");
    printf("  =================\n");

    suite_mood();
    suite_nodo();
    suite_sensores();
    suite_gfx();
    suite_render();
    suite_persona();
    suite_kip();
    suite_qr();
    suite_enlace();
    suite_red();
    suite_ota();
    suite_placa();

    return rk_t_report();
}
