ifbotech/root-kit/firmware/test/test_kip.c

/* Kip, dibujado con la lámina de Rocío (art/kip.c).
 *
 * Esta suite no mira pixeles —eso lo hace la regresión visual de
 * test_render—: mira la animación. Protege las dos promesas de su lámina:
 *
 *   1. QUE SEA FLUIDA. Ningún ciclo salta: ni entre clave y clave, ni al
 *      dar la vuelta, ni en la transición de un ánimo a cualquier otro. La
 *      boca sólo cambia de forma cerrada. Las cejas saltan, se pasan un poco
 *      y vuelven.
 *   2. QUE SEA SU LÁMINA. Cada ánimo que ella dibujó tiene en su pista lo
 *      que tiene en el papel: el guiño, la boqueada bajo el agua, la lengua
 *      afuera del calor, la mirada que busca la luz, las rendijas de reojo.
 */
#include <stddef.h>
#include "rk_test.h"
#include "../art/kip.h"
#include "../art/face.h"
#include "../core/persona.h"

#define PASO_MS 10u

static int absi(int v)
{
    return v < 0 ? -v : v;
}

static void pose(rk_kip_pose_t *p, rk_mood_t desde, rk_mood_t hacia, uint8_t mezcla,
                 uint32_t t)
{
    rk_kip_escena_t e;
    memset(&e, 0, sizeof e);
    e.desde = desde;
    e.hacia = hacia;
    e.mezcla = mezcla;
    e.t_ms = t;
    rk_kip_pose(p, &e);
}

static bool cerrado(const rk_kip_ojo_t *o)
{
    return o->a + o->b <= 0;
}

/* Lo más que se movió cada parte entre dos poses. */
typedef struct {
    int ojo, ceja, boca, mira, fx;
    bool estilo_abierto;    /* la boca cambió de forma estando abierta */
} salto_t;

static void medir(salto_t *s, const rk_kip_pose_t *a, const rk_kip_pose_t *b)
{
    int i, k;

    memset(s, 0, sizeof *s);
    for (i = 0; i < 2; i++) {
        const rk_kip_ojo_t *x = &a->ojo[i], *y = &b->ojo[i];
        const rk_kip_ceja_t *c = &a->ceja[i], *d = &b->ceja[i];
        int v[] = { x->a - y->a, x->b - y->b, x->incl - y->incl, x->dy - y->dy };
        int w[] = { c->dy - d->dy, c->ang - d->ang, c->arco - d->arco, c->grosor - d->grosor };
        for (k = 0; k < 4; k++) {
            if (absi(v[k]) > s->ojo) { s->ojo = absi(v[k]); }
            if (absi(w[k]) > s->ceja) { s->ceja = absi(w[k]); }
        }
    }
    {
        int v[] = { a->boca.abre - b->boca.abre, a->boca.curva - b->boca.curva,
                    a->boca.ancho - b->boca.ancho, a->boca.dy - b->boca.dy };
        for (k = 0; k < 4; k++) {
            if (absi(v[k]) > s->boca) { s->boca = absi(v[k]); }
        }
    }
    s->mira = absi(a->mira_x - b->mira_x) > absi(a->mira_y - b->mira_y)
            ? absi(a->mira_x - b->mira_x) : absi(a->mira_y - b->mira_y);
    for (k = 0; k < RK_KIP_FX_COUNT; k++) {
        if (absi(a->fx[k] - b->fx[k]) > s->fx) { s->fx = absi(a->fx[k] - b->fx[k]); }
    }
    s->estilo_abierto = a->boca.estilo != b->boca.estilo
                     && (a->boca.abre > 15 || b->boca.abre > 15);
}

/* ------------------------------------------------------- fluidez --- */
/* Cada ánimo, dos vueltas enteras de a 10 ms. Los topes son generosos a
 * propósito —un parpadeo es rápido y una mirada salta—: lo que buscan es
 * un corte, que es de otro orden (una clave que no empalma con la
 * siguiente, un ciclo que no vuelve a donde empezó). */
static void test_ciclos_fluidos(void)
{
    int m;
    char lbl[112];

    for (m = 0; m < RK_MOOD_COUNT; m++) {
        uint32_t per = rk_kip_periodo((rk_mood_t)m), t;
        rk_kip_pose_t a, b;
        salto_t peor, s;
        bool boca_ok = true;

        memset(&peor, 0, sizeof peor);
        pose(&a, (rk_mood_t)m, (rk_mood_t)m, 100u, 0u);
        for (t = PASO_MS; t <= 2u * per; t += PASO_MS) {
            pose(&b, (rk_mood_t)m, (rk_mood_t)m, 100u, t);
            medir(&s, &a, &b);
            if (s.ojo > peor.ojo) { peor.ojo = s.ojo; }
            if (s.ceja > peor.ceja) { peor.ceja = s.ceja; }
            if (s.boca > peor.boca) { peor.boca = s.boca; }
            if (s.mira > peor.mira) { peor.mira = s.mira; }
            if (s.estilo_abierto) { boca_ok = false; }
            a = b;
        }
        snprintf(lbl, sizeof lbl, "%s: los ojos no saltan (%d en 10 ms)", rk_mood_name((rk_mood_t)m), peor.ojo);
        CHECK_TRUE(lbl, peor.ojo <= 420);
        snprintf(lbl, sizeof lbl, "%s: las cejas no saltan (%d en 10 ms)", rk_mood_name((rk_mood_t)m), peor.ceja);
        CHECK_TRUE(lbl, peor.ceja <= 60);
        snprintf(lbl, sizeof lbl, "%s: la boca no salta (%d en 10 ms)", rk_mood_name((rk_mood_t)m), peor.boca);
        CHECK_TRUE(lbl, peor.boca <= 45);
        snprintf(lbl, sizeof lbl, "%s: la mirada no se teletransporta (%d en 10 ms)", rk_mood_name((rk_mood_t)m), peor.mira);
        CHECK_TRUE(lbl, peor.mira <= 1000);
        snprintf(lbl, sizeof lbl, "%s: la boca cambia de forma solo cerrada", rk_mood_name((rk_mood_t)m));
        CHECK_TRUE(lbl, boca_ok);
        snprintf(lbl, sizeof lbl, "%s: el ciclo vuelve a donde empezo", rk_mood_name((rk_mood_t)m));
        {
            rk_kip_pose_t x, y;
            pose(&x, (rk_mood_t)m, (rk_mood_t)m, 100u, 5u);
            pose(&y, (rk_mood_t)m, (rk_mood_t)m, 100u, per + 5u);
            CHECK_TRUE(lbl, memcmp(&x.ojo, &y.ojo, sizeof x.ojo) == 0 &&
                            memcmp(&x.boca, &y.boca, sizeof x.boca) == 0);
        }
    }
}

/* De cualquier ánimo a cualquier otro, de a un por ciento. */
static void test_transiciones_fluidas(void)
{
    int a, b, k, malas = 0, abiertas = 0;
    char lbl[112];

    for (a = 0; a < RK_MOOD_COUNT; a++) {
        for (b = 0; b < RK_MOOD_COUNT; b++) {
            rk_kip_pose_t p, q;
            pose(&p, (rk_mood_t)a, (rk_mood_t)b, 0u, 1200u);
            for (k = 1; k <= 100; k++) {
                salto_t s;
                pose(&q, (rk_mood_t)a, (rk_mood_t)b, (uint8_t)k, 1200u);
                medir(&s, &p, &q);
                if (s.ojo > 60 || s.ceja > 45 || s.boca > 25 || s.mira > 40 || s.fx > 20) {
                    malas++;
                    if (malas < 4) {
                        snprintf(lbl, sizeof lbl, "%s -> %s salta en %d%%", rk_mood_name((rk_mood_t)a),
                                 rk_mood_name((rk_mood_t)b), k);
                        rk_t_fail(lbl, "la transicion tiene un corte");
                    }
                }
                if (s.estilo_abierto) {
                    abiertas++;
                }
                p = q;
            }
        }
    }
    CHECK_INT("ninguna transicion entre animos tiene un corte", 0, malas);
    CHECK_INT("y en ninguna la boca cambia de forma abierta", 0, abiertas);

    /* Los extremos son los ánimos puros. */
    {
        rk_kip_pose_t p, q;
        pose(&p, RK_MOOD_HAPPY, RK_MOOD_DROWNING, 100u, 700u);
        pose(&q, RK_MOOD_DROWNING, RK_MOOD_DROWNING, 100u, 700u);
        CHECK_TRUE("en 100 es el destino", memcmp(&p, &q, sizeof p) == 0);
        pose(&p, RK_MOOD_HAPPY, RK_MOOD_DROWNING, 50u, 700u);
        CHECK_TRUE("a mitad de camino el agua va por la mitad",
                   p.fx[RK_KIP_FX_AGUA] > 300 && p.fx[RK_KIP_FX_AGUA] < 700);
    }
}

/* ------------------------------------------------ las cejas saltan --- */
static void test_cejas_saltonas(void)
{
    uint32_t t;
    int minimo = 0, final;
    rk_kip_pose_t p;

    /* En el guiño la ceja derecha sube de 0 a -70: tiene que pasarse de
     * largo y volver, no llegar justo. */
    for (t = 5300u; t <= 5800u; t += 5u) {
        pose(&p, RK_MOOD_HAPPY, RK_MOOD_HAPPY, 100u, t);
        if (p.ceja[1].dy < minimo) {
            minimo = p.ceja[1].dy;
        }
    }
    pose(&p, RK_MOOD_HAPPY, RK_MOOD_HAPPY, 100u, 6500u);
    final = p.ceja[1].dy;
    CHECK_TRUE("la ceja del guino se pasa de largo al saltar", minimo < final - 3);
    CHECK_NEAR("y vuelve a su lugar", -70, final, 3);

    /* Los cejazos: en contento, a los dos segundos las dos suben un
     * instante y bajan. */
    {
        rk_kip_pose_t antes, arriba, despues;
        pose(&antes, RK_MOOD_HAPPY, RK_MOOD_HAPPY, 100u, 1990u);
        pose(&arriba, RK_MOOD_HAPPY, RK_MOOD_HAPPY, 100u, 2150u);
        pose(&despues, RK_MOOD_HAPPY, RK_MOOD_HAPPY, 100u, 2600u);
        CHECK_TRUE("en un cejazo las cejas suben",
                   arriba.ceja[0].dy < antes.ceja[0].dy - 30 && arriba.ceja[1].dy < antes.ceja[1].dy - 30);
        CHECK_TRUE("y despues bajan", absi(despues.ceja[0].dy - antes.ceja[0].dy) <= 2);
    }
}

/* --------------------------------------------- la lámina, en la pista --- */
typedef struct {
    bool guino, teal, dientes, linea, grito_grande, lengua, o, beso, onda, rojo;
    bool siempre_agua, siempre_sumergida, siempre_mira_abajo, siempre_cerrados;
    bool cerrado_alguna_vez;
    int abre_min, abre_max, mira_x_min, mira_x_max, mira_y_max, a_max, rendija_max;
    int tupido_min;
} recorrido_t;
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
